animaro/Brick-Lamp/IMG_5560.JPG

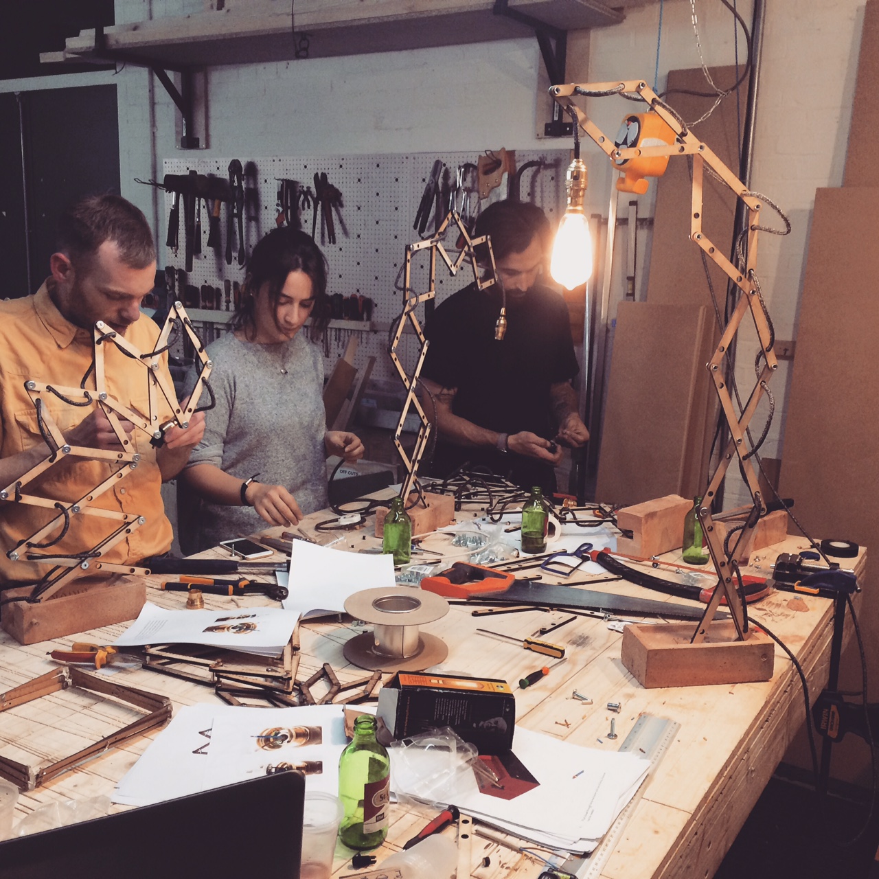
IMG_5560.JPG
